jinyalong/NixieFriday/SoftWare/ssd1306.py

from micropython import const
import time
import framebuf
import sys
# 48x70
wifi_large = [
0x00,0x00,0x00,0x00,0x00,0x00,0x00,0x00,0x00,0x00,0x00,0x00,0x00,0x00,0x00,0x00,
0x00,0x00,0x80,0xC0,0xE0,0xF0,0xF0,0xF8,0xFC,0xFC,0xFC,0xFE,0xFE,0xFE,0xFF,0xFF,
0xFF,0xFF,0xFF,0xFF,0xFF,0xFF,0xFF,0xFF,0xFE,0xFE,0xFE,0xFC,0xFC,0xFC,0xF8,0xF0,
0xF0,0xE0,0xC0,0x80,0x00,0x00,0x00,0x00,0x00,0x00,0x00,0x00,0x00,0x00,0x00,0x00,
0x00,0x00,0x00,0x00,0x00,0x00,0x00,0x80,0xE0,0xF0,0xF0,0xF8,0xFC,0xFC,0xFE,0xFE,
0xFE,0xFE,0xFE,0xFE,0xFE,0xFE,0xFE,0xFF,0xFF,0xFF,0xFF,0xFF,0xFF,0xFF,0xFF,0xFF,
0xFF,0xFF,0x7F,0xFF,0xFF,0xFF,0xFF,0xFF,0xFF,0xFF,0xFF,0xFF,0x7F,0x3F,0x1F,0x1F,
0x0F,0x0F,0x0F,0x0F,0x0F,0x0F,0x0F,0x07,0x0F,0x07,0x07,0x06,0x06,0x06,0x06,0x0E,
0x0E,0x8E,0x0E,0x0E,0x0C,0x1C,0x38,0x70,0xF0,0xE0,0x80,0x00,0xFE,0xFF,0xFF,0xFF,
0xFF,0xFF,0xF8,0x80,0x00,0x00,0x03,0xFF,0x1F,0x01,0x00,0x00,0x00,0x03,0xFF,0x1F,
0x01,0x00,0x00,0xE0,0xFF,0xFF,0x1C,0x18,0x18,0x18,0xFD,0xFF,0xFF,0xFF,0xFF,0xFF,
0xFF,0x00,0x00,0x00,0x00,0x00,0xFF,0xFF,0xFF,0xFF,0x8F,0x8F,0x8F,0x8F,0x8F,0x8F,
0x8F,0x8F,0x0F,0x00,0x00,0x02,0xE7,0xE7,0xE7,0xE7,0x00,0x00,0x00,0x00,0x01,0x3F,
0xFF,0xFE,0xFF,0xFF,0xFF,0xFF,0xFF,0xFF,0xFF,0xFF,0xF8,0x80,0x00,0x00,0x00,0x80,
0xFC,0xFF,0xE0,0x00,0x00,0x00,0x00,0xE0,0xFE,0xFF,0xFF,0xFF,0x80,0x00,0x00,0x00,
0xFF,0xFF,0xFF,0xFF,0xFF,0xFF,0x00,0x00,0x00,0x00,0x00,0x00,0xFF,0xFF,0xFF,0xFF,
0x07,0x07,0x07,0x07,0x07,0x07,0x07,0x07,0x00,0x00,0x00,0x00,0xFF,0xFF,0xFF,0x7F,
0x00,0x00,0x00,0x00,0x00,0xF0,0xFF,0xFF,0x00,0x03,0x07,0x0F,0x1F,0x3F,0x7F,0x7F,
0x7F,0xFF,0xFF,0xFF,0xFF,0xFF,0xFF,0xFF,0xFF,0xFF,0xFF,0xFF,0xFF,0xFF,0xFF,0xFF,
0xFF,0xFF,0xFF,0xFF,0xFF,0xFF,0xFF,0xFF,0xDF,0xCF,0xC3,0xC0,0xC0,0xC0,0xC0,0xC0,
0xC0,0xC0,0xC0,0xC0,0xC0,0xC0,0xC0,0xC0,0xC0,0xC0,0xC0,0xC0,0xC0,0xC0,0xC0,0xC0,
0xC0,0xE0,0xE0,0xE0,0xE0,0x60,0x70,0x70,0x38,0x1C,0x0E,0x07,0x03,0x00,0x00,0x00,
0x00,0x00,0x00,0x00,0x00,0x00,0x00,0x00,0x00,0x00,0x00,0x00,0x00,0x00,0x00,0x01,
0x01,0x03,0x07,0x0F,0x1F,0x1F,0x3F,0x3F,0x7F,0x7F,0x7F,0x7F,0xFF,0xFF,0xFF,0xFF,
0xFF,0xFF,0xFF,0xFF,0xFF,0xFF,0x7F,0x7F,0x7F,0x3F,0x3F,0x3F,0x1F,0x1F,0x0F,0x07,
0x03,0x01,0x01,0x00,0x00,0x00,0x00,0x00,0x00,0x00,0x00,0x00,0x00,0x00,0x00,0x00,
0x00,0x00,0x00,0x00]

bluetooth = [0x10,0x30,0x40,0xFF,0xCE,0x4C,0x38,0x10,0x0C,0x06,0x02,0xFF,0x73,0x32,0x1C,0x00]

wifi = [0x10,0x38,0x3C,0x1C,0x8E,0x8E,0xC7,0xC7,0xE7,0xE7,0xE7,0xC7,0xC7,0x8E,0x8E,0x1C,
	0x3C,0x38,0x10,0x00,0x00,0x00,0x00,0x01,0x03,0x01,0x70,0xF8,0xF8,0xF8,0x70,0x01,
	0x03,0x01,0x00,0x00,0x00,0x00]
  
alarmclock = [0x8C,0xF6,0x1B,0x0D,0x06,0x02,0x02,0xFA,0x82,0x82,0x06,0x0D,0x1B,0xF6,0x8C,0x01,
	0x8F,0x78,0x30,0x60,0x40,0x40,0x41,0x41,0x41,0x60,0x30,0x78,0x8F,0x01]
  
  
BlueTooth_X = 72
Wifi_X = 85
AlarmClock_X = 109

currentBoard=""
if(sys.platform=="esp8266"):
  currentBoard="esp8266"
elif(sys.platform=="esp32"):
  currentBoard="esp32"
elif(sys.platform=="pyboard"):
  currentBoard="pyboard"
  import pyb
# register definitions
SET_CONTRAST        = const(0x81)
SET_ENTIRE_ON       = const(0xa4)
SET_NORM_INV        = const(0xa6)
SET_DISP            = const(0xae)
SET_MEM_ADDR        = const(0x20)
SET_COL_ADDR        = const(0x21)
SET_PAGE_ADDR       = const(0x22)
SET_DISP_START_LINE = const(0x40)
SET_SEG_REMAP       = const(0xa0)
SET_MUX_RATIO       = const(0xa8)
SET_COM_OUT_DIR     = const(0xc0)
SET_DISP_OFFSET     = const(0xd3)
SET_COM_PIN_CFG     = const(0xda)
SET_DISP_CLK_DIV    = const(0xd5)
SET_PRECHARGE       = const(0xd9)
SET_VCOM_DESEL      = const(0xdb)
SET_CHARGE_PUMP     = const(0x8d)
class SSD1306:
  def __init__(self, width, height, external_vcc):
    self.width = width
    self.height = height
    self.external_vcc = external_vcc
    self.pages = self.height // 8
    self.buffer = bytearray(self.pages * self.width)
    self.framebuf = framebuf.FrameBuffer(self.buffer, self.width, self.height, framebuf.MVLSB)
    self.poweron()
    self.init_display()
  def init_display(self):
    for cmd in (
      SET_DISP | 0x00, # off
      # address setting
      SET_MEM_ADDR, 0x00, # horizontal
      # resolution and layout
      SET_DISP_START_LINE | 0x00,
      SET_SEG_REMAP | 0x01, # column addr 127 mapped to SEG0
      SET_MUX_RATIO, self.height - 1,
      SET_COM_OUT_DIR | 0x08, # scan from COM[N] to COM0
      SET_DISP_OFFSET, 0x00,
      SET_COM_PIN_CFG, 0x02 if self.height == 32 else 0x12,
      # timing and driving scheme
      SET_DISP_CLK_DIV, 0x80,
      SET_PRECHARGE, 0x22 if self.external_vcc else 0xf1,
      SET_VCOM_DESEL, 0x30, # 0.83*Vcc
      # display
      SET_CONTRAST, 0xff, # maximum
      SET_ENTIRE_ON, # output follows RAM contents
      SET_NORM_INV, # not inverted
      # charge pump
      SET_CHARGE_PUMP, 0x10 if self.external_vcc else 0x14,
      SET_DISP | 0x01): # on
      self.write_cmd(cmd)
    self.fill(0)
    self.show()
  def fill(self, col):
    self.framebuf.fill(col)
  def poweroff(self):
    self.write_cmd(SET_DISP | 0x00)
  def contrast(self, contrast):
    self.write_cmd(SET_CONTRAST)
    self.write_cmd(contrast)
  def invert(self, invert):
    self.write_cmd(SET_NORM_INV | (invert & 1))
  def show(self):
    x0 = 0
    x1 = self.width - 1
    if self.width == 64:
      # displays with width of 64 pixels are shifted by 32
      x0 += 32
      x1 += 32
    self.write_cmd(SET_COL_ADDR)
    self.write_cmd(x0)
    self.write_cmd(x1)
    self.write_cmd(SET_PAGE_ADDR)
    self.write_cmd(0)
    self.write_cmd(self.pages - 1)
    self.write_data(self.buffer)
  def wifi_on(self):
    for i in range(0,38):
      self.buffer[i//19*128+i%19+Wifi_X] = wifi[i]
    self.show() 
  def wifi_off(self):
    for i in range(0,38):
      self.buffer[i//19*128+i%19+Wifi_X] = 0
    self.show() 
  def alarm_clock_on(self):
    for i in range(0,30):
      self.buffer[i//15*128+i%15+AlarmClock_X] = alarmclock[i]
    self.show() 
  def alarm_clock_off(self):
    for i in range(0,30):
      self.buffer[i//15*128+i%15+AlarmClock_X] = 0  
    self.show() 
  def show_logo(self):
    self.fill(0)
    for i in range(0,1024):
      self.buffer[i] = logo[i]
    self.show()
  def show_powered_by(self):
    self.fill(0)
    self.text("powered by",24,20,1)
    self.text("CodeFriday",24,45,1)
    self.show()
  def showBigWifiLogo(self):
    self.fill(0)
    for i in range(0,420):
      self.buffer[(i//70+1)*128+i%70+29] = wifi_large[i]
    self.show()
  def showDateWeekDay(self,var1,var2):
    for i in range(256,1024):
      self.buffer[i] = 0
    self.text(var1,24,20)
    self.text(var2,32,40)
    self.show()
  def text(self, string, x, y, col=1):
      self.framebuf.text(string, x, y, col)
  def ap_msg(self):
    self.fill(0)
    self.text('WIFI:IN14_CLOCK',4,7)
    self.text('pwd:12345678',16,21)
    self.text('192.168.4.1',20,35)
    self.text('open in browser',4,49)
    self.show()  
  def ota_updating(self):
    self.fill(0)
    self.text('OTA updating...',4,8)
    self.text('please waite',16,24)
    self.text('about 3~5 mins',8,40)
    self.show() 
  def ota_updating_res(self, val):
    self.fill(0)
    if val == True:
      self.text('OTA update',24,8)
      self.text('success',36,16)
      self.text('>>now version<<',4,32)
      self.text('v1.0',48,44)
      self.show()
    elif val == False:
      self.text('OTA update error',0,20)
      self.text('check your wifi',4,40)
      self.show()
  def mqtt_connecting(self):
    self.fill(0)
    self.text('try to connect',4,22)
    self.text('mqtt server...',8,34)
    self.show()
  def mqtt_connect_res(self, val):
    self.fill(0)
    if val == True:
      self.text('mqtt connect',16,22)
      self.text('success',36,34)
    elif val == False:
      self.text('mqtt connect',16,22)
      self.text('false',44,34)
    self.show()
class SSD1306_I2C(SSD1306):
  def __init__(self, width, height, i2c, addr=0x3c, external_vcc=False):
    self.i2c = i2c
    self.addr = addr
    self.temp = bytearray(2)
    super().__init__(width, height, external_vcc)
  def write_cmd(self, cmd):
    self.temp[0] = 0x80 # Co=1, D/C#=0
    self.temp[1] = cmd
    #IF SYS  :
    global currentBoard
    if currentBoard=="esp8266" or currentBoard=="esp32":
      self.i2c.writeto(self.addr, self.temp)
    elif currentBoard=="pyboard":
      self.i2c.send(self.temp,self.addr)
    #ELSE:
          
  def write_data(self, buf):
    self.temp[0] = self.addr << 1
    self.temp[1] = 0x40 # Co=0, D/C#=1
    global currentBoard
    if currentBoard=="esp8266" or currentBoard=="esp32":
      self.i2c.start()
      self.i2c.write(self.temp)
      self.i2c.write(buf)
      self.i2c.stop()
    elif currentBoard=="pyboard":
      #self.i2c.send(self.temp,self.addr)
      #self.i2c.send(buf,self.addr)
      self.i2c.mem_write(buf,self.addr,0x40)
  def poweron(self):
    pass
